The-XOR/Smistarumori/schema elettrificato/7404.jpg

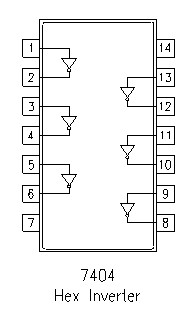
schema elettrificato/7404.jpg
