The-XOR/Smistarumori/schema elettrificato/rele/rele.kicad_pcb

## KiCad design kicad/opentDCS.kicad_sch

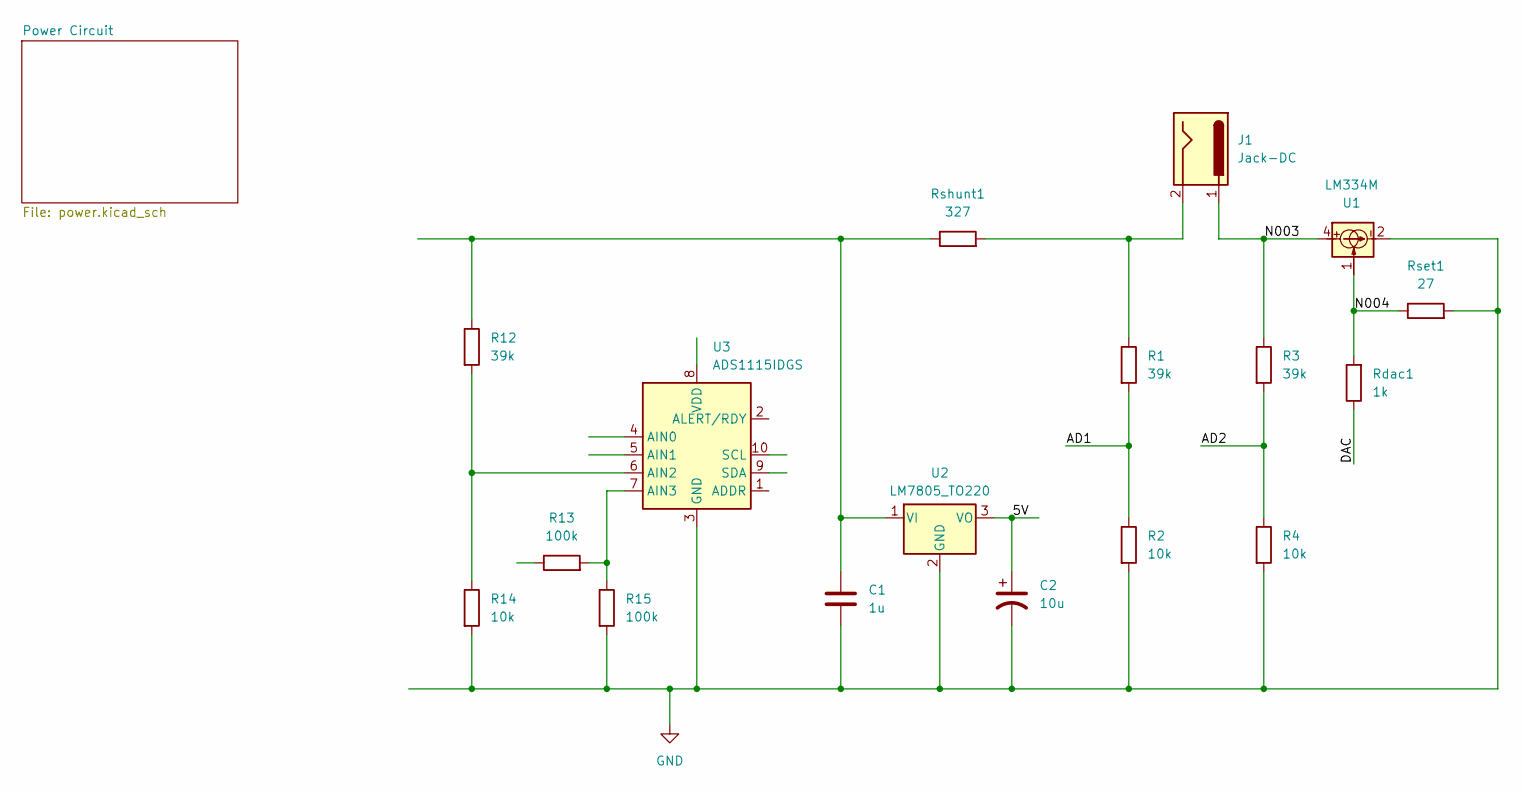
[picture p17: schematic opentDCS.kicad_sch]

Parts:
C1: 1u
C2: 10u
J1: Jack-DC
R1, R3, R12: 39k
R2, R4, R14: 10k
R13, R15: 100k
Rdac1: 1k
Rset1: 27
Rshunt1: 327
U1: LM334M; SOIC-8_3.9x4.9mm_P1.27mm
U2: LM7805_TO220; TO-220-3_Vertical
U3: ADS1115IDGS; TSSOP-10_3x3mm_P0.5mm

Connections:
5V: C2.1, U2.3 (VO)
AD1: R1.2, R2.1
AD2: R3.2, R4.1
DAC: Rdac1.1
GND: C1.2, C2.2, R2.2, R4.2, R14.2, R15.2, Rset1.2, U1.2, U1.3, U1.6, U1.7, U2.2 (GND), U3.3 (GND)
N003: J1.1, R3.1, U1.4
N004: Rdac1.2, Rset1.1, U1.1
unnamed: C1.1, R12.1, Rshunt1.1, U2.1 (VI)
unnamed: J1.2, R1.1, Rshunt1.2
unnamed: R12.2, R14.1, U3.6 (AIN2)
unnamed: R13.2, R15.1, U3.7 (AIN3)
